stuart2307/SCARAB/Documents/SCARAB Device.png

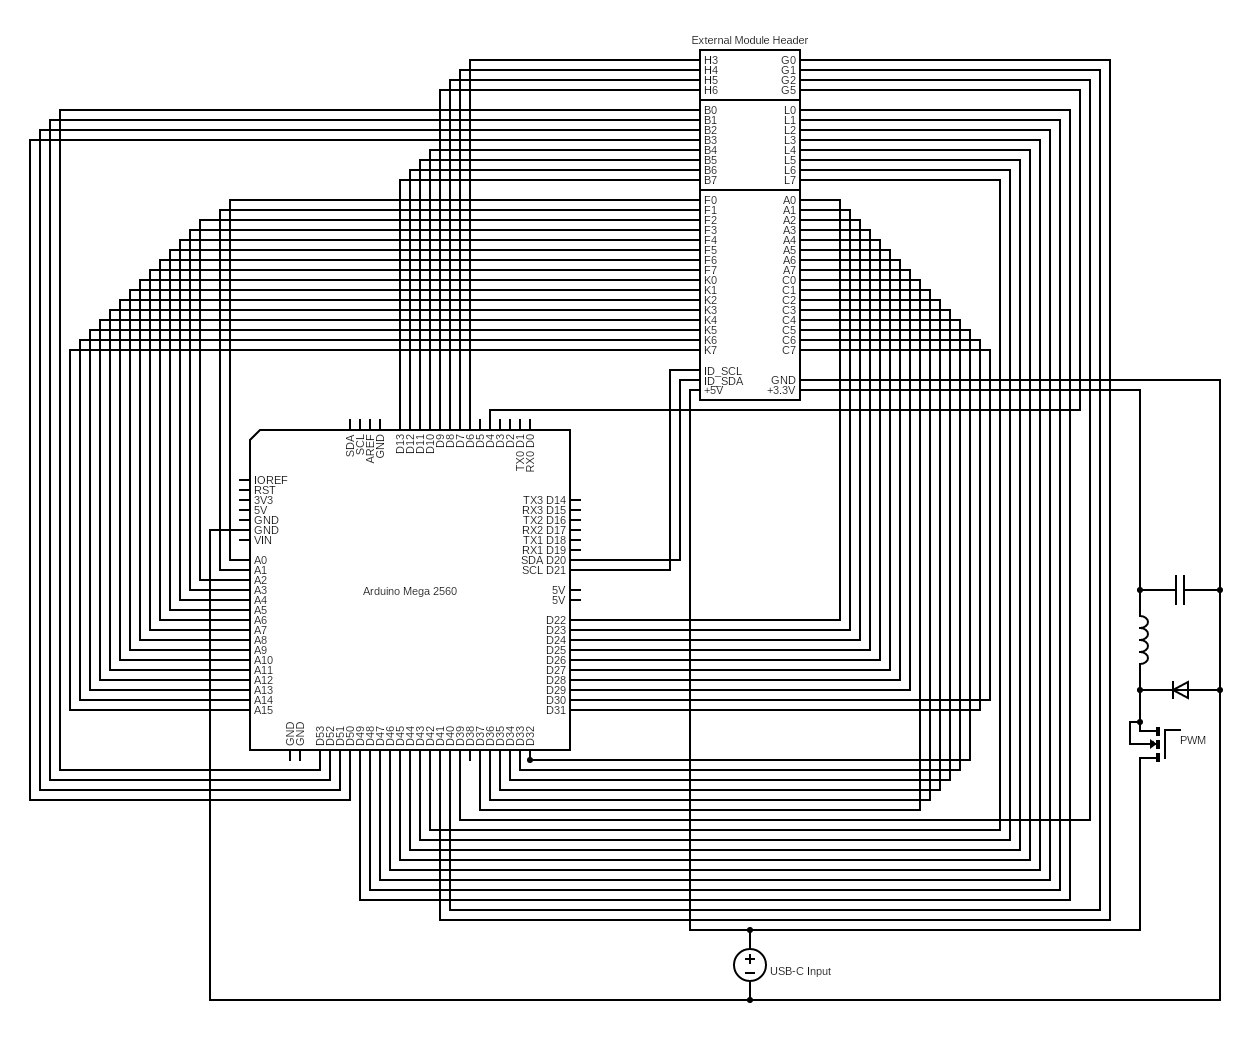
Documents/SCARAB Device.png
