stuart2307/SCARAB/Documents/SCARAB GBA Module.png

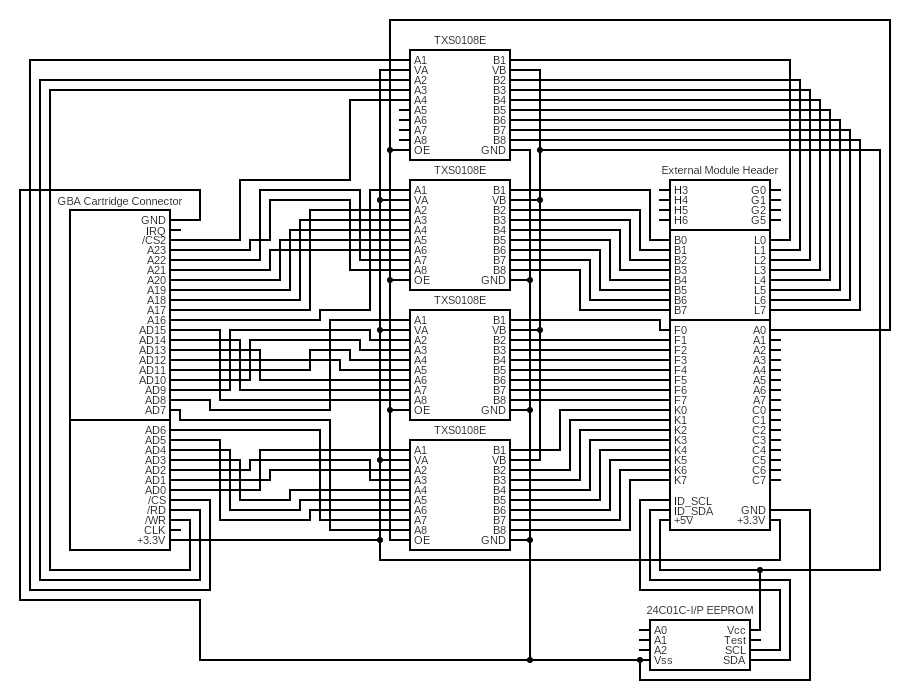
Documents/SCARAB GBA Module.png
