stuart2307/SCARAB/Documents/SCARAB N64 Module.png

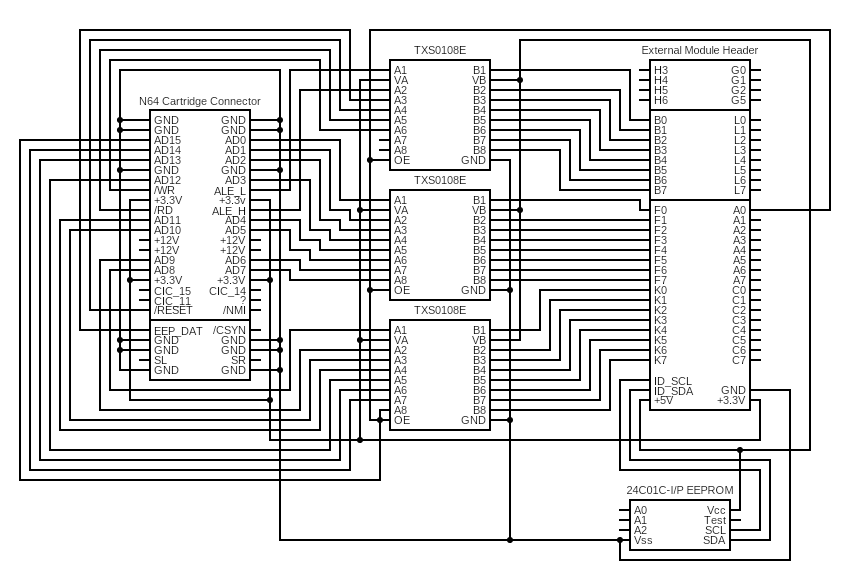
Documents/SCARAB N64 Module.png
