stuart2307/SCARAB/Documents/SCARAB NES Module.png

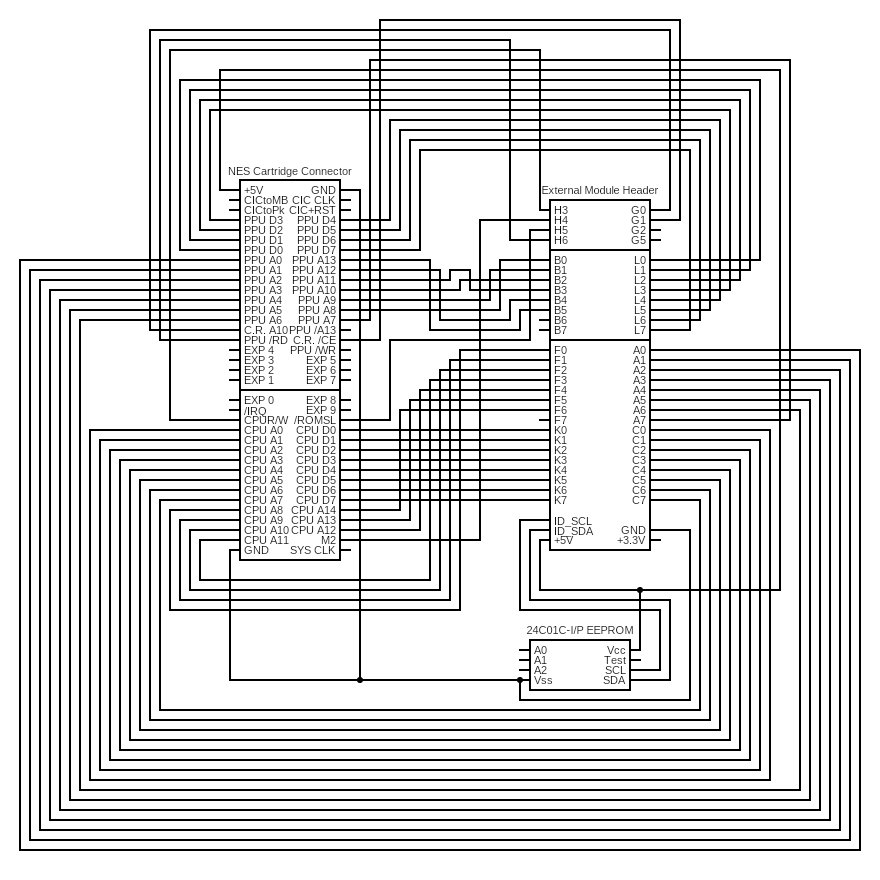
Documents/SCARAB NES Module.png
