stuart2307/SCARAB/Documents/SCARAB SNES Module.png

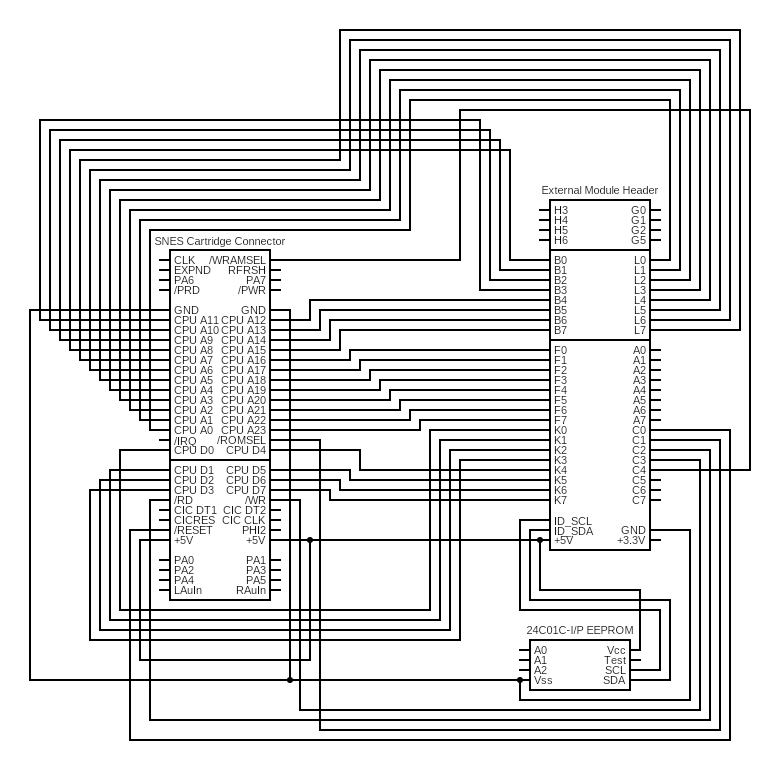
Documents/SCARAB SNES Module.png
